nikander/VINK/R1S1B/iges/R1B/geom.rotor.ug-Surface-Blade-typ1.igs

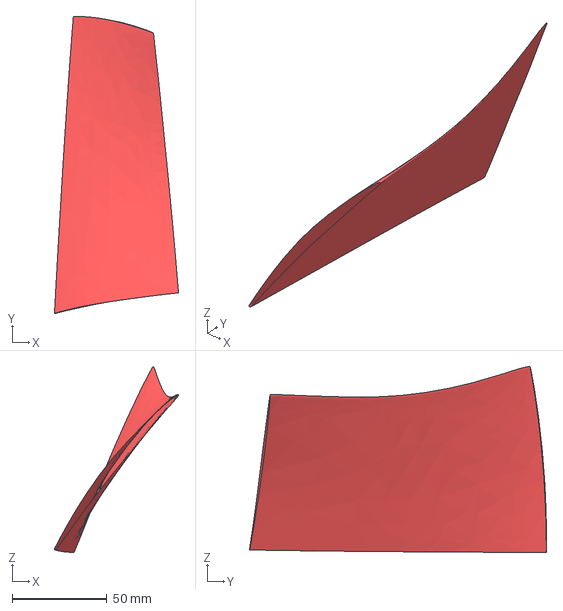
[picture p21: CAD file, 2016-11-21]
R1S1B/iges/R1B/geom.rotor.ug-Surface-Blade-typ1.igs
65.4 x 156.5 x 98.1 mm
